tonykoop/handpan/validation-loop.csv

check_id | packet_artifact | readiness_before | prediction_source | target | tolerance | method | measured_result | status | next_action | evidence | source_status
vl001 | handpan-design-table.xlsx | L1_packet | workbook shell inputs | Top and bottom shell diameter, height, mass, and 1.0 mm thickness map recorded before forming | measurement_required | Measure diameter/height with tape or calipers, mass with scale, and thickness on a marked grid | TBD | measurement_required | Create a shell inspection log before any forming or tone-field work | issue #1 | prototype_not_measured
vl002 | family-spec.csv | L1_packet | material path assumption | Material and heat/surface treatment path is documented per shell | pass_fail_review | Collect supplier certificate or process notes for nitrided DC04, stainless, or alternate shell stock | TBD | measurement_required | Attach supplier/process evidence and branch stainless/nitrided paths separately | issue #1 | supplier_spec_unverified
vl003 | drawings/01-top-layout.svg | L1_packet | first-pass layout estimate | Ding and eight surrounding field marks are removable templates only | pass_fail_review | Lay out on removable film/template and photograph before hammering; do not scribe final cut/tuned geometry | TBD | measurement_required | Have a tuner or forming lead approve template placement before field forming | issue #1 | tuner_review_required
vl004 | measured-partial-strike-log.csv | L1_packet | coupled plate first-order model | Each tuned field has fundamental, octave, and compound-fifth partial captures | measurement_required | Record FFT/strobe captures for Ding and fields A3 through A4 at fixed mic distance and strike force; store rows in measured-partial-strike-log.csv | TBD | measurement_required | Populate measured fundamentals/partials before claiming tuning success | issue #7 | prototype_not_measured
vl005 | measured-partial-strike-log.csv | L1_packet | tuner-led tuning workflow | Cross-talk matrix is recorded after rough tuning and after final settle | measurement_required | Strike every field and record neighbor response in dB relative to struck fundamental; duplicate cross-talk matrix rows in measured-partial-strike-log.csv | TBD | measurement_required | Add strike matrix and retune fields that exceed the cross-talk gate | issue #7 | prototype_not_measured
vl006 | design.md | L1_packet | Gu Helmholtz sanity check | Actual Gu response is measured after shell closure | measurement_required | Measure Gu/cavity response with tap, air excitation, or spectrum capture after rim bonding | TBD | measurement_required | Update Gu model with measured shell volume, port diameter, lip shape, and response | issue #1 | prototype_not_measured
vl007 | assembly-manual.md | L1_packet | forming and hammering sequence | Forming, work-hardening, and heat-treatment changes are logged by operation | measurement_required | Log hammering passes, heat/surface treatment, rest times, and recheck tuning after each major operation | TBD | measurement_required | Create a build log before treating field geometry as repeatable | issue #1 | process_unverified
vl008 | risks.md | L1_packet | safety/public-release gates | Human handpan tuner and metal-forming lead review the packet and first measurements | pass_fail_review | Review layout, forming sequence, material/process path, Gu edge safety, and public claims | TBD | measurement_required | Keep the repo in research/private-review posture until signoff is recorded | issue #1 | human_review_required
vl009 | data/measured-partial-log.csv | L2_packet | issue #7 measurement protocol | Every field has one row per measured partial role with strike, mic, environment, file reference, and reviewer status | measurement_required | Capture controlled strikes and FFT/strobe evidence before entering measured values | TBD | measurement_required | Populate measured-partial log before claiming field tuning or partial balance | issue #7 | prototype_not_measured
vl010 | data/cross-talk-strike-log.csv | L2_packet | issue #7 measurement protocol | Every struck field records listener field response relative to the struck field | measurement_required | Run controlled strike matrix at the same gain and mic posture after rough tune and after final settle | TBD | measurement_required | Populate cross-talk strike log before claiming isolation or low cross-talk | issue #7 | prototype_not_measured
vl011 | validation-report.md | L2_packet | V5 honesty rule | Targets are labeled target/concept/pending_measurement until matching log evidence exists | pass_fail_review | Review README, design, print packet, site, and issue text against data logs | TBD | measurement_required | Block public/build-ready wording until the measured logs and specialist review support it | issue #7 | honesty_gate_required
vl012 | drawings/issue-4-dimple-layout-vector-test.md | L1_packet | issue #4 Illustrator-MCP vector-test brief | Dimple layout vector output is registered as pending_measurement and blocked until measured shell data plus tuner review exist | pass_fail_review | Run Illustrator MCP only after shell diameter/profile/thickness map and human layout review are recorded; verify output against register before any SVG/DXF export is promoted | TBD | measurement_required | Do not generate or use vector coordinates from concept SVGs; keep issue #4 at pending authority until MCP and measurement evidence exist | issue #4 | mcp_and_measurement_required
